brotulix/arduino-sequencer/solidedge/Labels/13V8DC.png

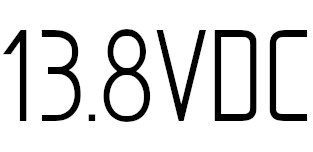
solidedge/Labels/13V8DC.png
