brotulix/arduino-sequencer/solidedge/Labels/144.png

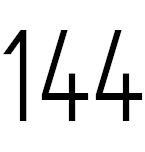
solidedge/Labels/144.png
