brotulix/arduino-sequencer/solidedge/Labels/432.png

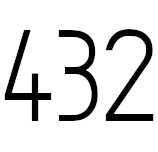
solidedge/Labels/432.png
