brotulix/arduino-sequencer/solidedge/Labels/Coax A.png

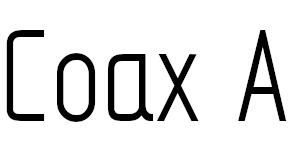
solidedge/Labels/Coax A.png
