brotulix/arduino-sequencer/solidedge/Labels/Coax C.png

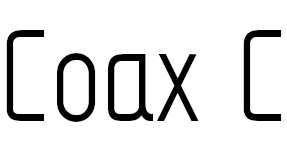
solidedge/Labels/Coax C.png
