brotulix/arduino-sequencer/solidedge/Labels/PA PTT nonfat.png

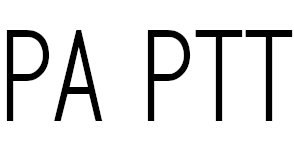
solidedge/Labels/PA PTT nonfat.png
