brotulix/arduino-sequencer/solidedge/Labels/Power.png

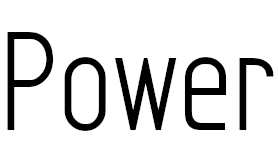
solidedge/Labels/Power.png
