brotulix/arduino-sequencer/solidedge/Labels/Preamp.png

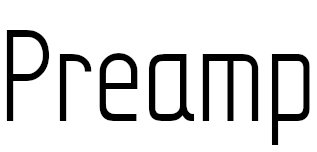
solidedge/Labels/Preamp.png
