brotulix/arduino-sequencer/solidedge/Labels/Radio TX.png

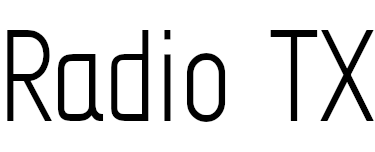
solidedge/Labels/Radio TX.png
