brotulix/arduino-sequencer/solidedge/Labels/Radio.png

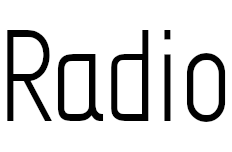
solidedge/Labels/Radio.png
