brotulix/arduino-sequencer/solidedge/Labels/RX-TX.png

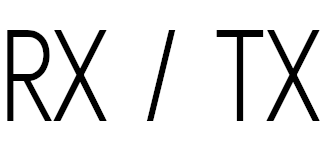
solidedge/Labels/RX-TX.png
