brotulix/arduino-sequencer/solidedge/Labels/TX Inhibit.png

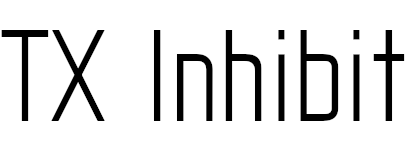
solidedge/Labels/TX Inhibit.png
